MBascoy/Learning-Numbers/3D design/anchors/anchor_pcb.scad

include<../global_constants.scad>

anchor_height=4;

top_y=-38;
bottom_y=-105;

left_anchor_x = anchor_outer_size + button_starting_x - (anchor_outer_size - anchor_inner_size) + button_size;

right_anchor_x = body_size - anchor_outer_size - button_size;

top_right_anchor_x = confirm_button_x + anchor_inner_size;

top_left_anchor_x = screen_x - anchor_outer_size*2;

module anchor_pcb(){
    
    //top left anchor
    base_anchor(top_left_anchor_x, top_y -anchor_inner_size);
    
    //bottom left anchor
    base_anchor(left_anchor_x, bottom_y);
    
    //top right anchor
    base_anchor(top_right_anchor_x, top_y -anchor_inner_size);
    
    //bottom right anchor
    base_anchor(right_anchor_x, bottom_y);
}

module base_anchor(x, y){
        translate([x, y, -wall_size_offset_x +cylinder_radius - anchor_height])
    difference(){
        cylinder(anchor_height, anchor_outer_size, anchor_outer_size);
        cylinder(anchor_height, anchor_inner_size, anchor_inner_size - anchor_inner_size_margin);
    }
}
