MBascoy/Learning-Numbers/3D design/body/holes/buttons_counting.scad

include<../../global_constants.scad>

module buttons_counting(){
        
        //buttons
        for(i=[0:1:7]){
            translate([(button_x_placement*i)+button_starting_x, button_y_placement, cylinder_radius-button_size])cube(button_size);
        }
        
        for(i=[0:1:7]){
            translate([(button_x_placement*i)+button_starting_x, button_y_placement-button_y_second_row, cylinder_radius-button_size])cube(button_size);
        }
        
        //leds
        led_starting_x=button_starting_x + (button_size/2);
        
        led_x_placement=button_size + button_x_margin;
        led_y_placement=-82;
        led_y_second_row=30;
        
        
        for(i=[0:1:7]){
            translate([(led_x_placement*i)+led_starting_x, led_y_placement, cylinder_radius-led_height])cylinder(led_height, led_size, led_size);
        }
        
        for(i=[0:1:7]){
            translate([(led_x_placement*i)+led_starting_x, led_y_placement-led_y_second_row, cylinder_radius-led_height])cylinder(led_height, led_size, led_size);
        }
        
        
        //confirm button
        translate([confirm_button_x, confirm_button_y, cylinder_radius-button_size])cube(button_size);
        
}
