MBascoy/Learning-Numbers/3D design/body/holes/screen.scad

include<../../global_constants.scad>

module screen(){
        translate([screen_x, screen_y, cylinder_radius-screen_size])cube([screen_size*2, screen_size, screen_size]);
}
